kajusK/Darkstar-Mk.II/avr/src/modes/caving.c

/*
 * Caving mode
 *
 * For license, see LICENSE.txt
 *
 * Jakub Kaderka 2017
 */

#include <inttypes.h>
#include <string.h>

#include "system.h"
#include "buttons.h"
#include "light.h"

struct s_levels {
	uint8_t flood;
	uint8_t spot;
	uint8_t red;
	uint8_t white;
};

struct s_config {
	uint16_t magic;
	uint8_t num_levels;
	uint8_t prg_locked : 1;
	uint8_t light_control : 2;
};

enum e_mode {
	NORMAL,
	PROGRAMMING,
	LOCKED,
	CONFIGURATION,
	CONFIGURATION_ENTRY,	//entering config mode, ignore buttons
};

#define BUTTON_UP BUTTON1
#define BUTTON_DOWN BUTTON2

//time in tenths of ms to be considered as holding
#define HOLD_TIME 50

//time spent in mode=0 to go to sleep
#define OFF_TIME 200

//inactivity before returning from programming mode
#define TIMER_MAX 150

//voltage levels to report
#define VOLTAGE_4	3700
#define VOLTAGE_3	3500	//limit 1
#define VOLTAGE_2	3300	//limit 2
#define VOLTAGE_1	3100	//limit 3

//temperature limits
#define TEMP_LIM_START	40	//enable limiting above this temperature
#define TEMP_LIM_AGGRESIVE	45	//limit more aggresive above this temperature
#define TEMP_LIM_MIN	30	//don't limit below this level

//minimum settable light level
#define LIGHT_MIN 1
//increase by this value in programming mode
#define LIGHT_STEP 50

#define DEF_LEVELS 7
#define MAX_LEVELS 10

// magic value to determine if config is already in eeprom
#define MAGIC 0xBEEF

const struct s_levels def_levels[] = {{0, 0, 0, 0}, // off - must be here
				      {0, 0, 1, 0}, //red only
				      {LIGHT_MIN, 0, 0, 0}, //low spot
				      {LIGHT_STEP, LIGHT_STEP, 0, 0}, //small spaces
				      {100, 50, 0, 0}, //normal walking
				      {70, 200, 0, 0}, //distance
				      {255, 255, 0, 0}}; //photo

//limit levels for low voltage (from lowest to full battery)
const uint8_t limits[5] = {50, 120, 160, 230, 255};

static struct s_levels levels[MAX_LEVELS];
static struct s_config config = { MAGIC, DEF_LEVELS, 0, MODE_NORMAL };

static uint8_t cur_levels;
static enum e_mode cur_mode;

static uint8_t hold_done;
static uint8_t timer;

static void config_load(void)
{
	int i;

	config_read(0, (uint8_t *)&config, sizeof(config));
	config_read(sizeof(config), (uint8_t *)&levels, sizeof(levels[0])*config.num_levels);

	//if mode is completely empty (e.g. corrupted memory), turn flood on
	for (i = 1; i < config.num_levels; i++) {
		if (levels[i].white == 0 && levels[i].red == 0 && levels[i].flood == 0 && levels[i].spot == 0)
			levels[i].flood = LIGHT_MIN;
	}
}

static void config_save(void)
{
	config_write(0, (uint8_t *)&config, sizeof(config));
	config_write(sizeof(config), (uint8_t *)&levels, sizeof(levels[0])*config.num_levels);
}

static void config_default(void)
{
	memcpy(&levels, &def_levels, DEF_LEVELS*sizeof(def_levels[0]));
	config.num_levels = DEF_LEVELS;
	config_save();
}

/*
 * Get current voltage rating
 */
static uint8_t rate_voltage(void)
{
	uint16_t voltage = system_voltage();

	if (voltage < VOLTAGE_1)
		return 0;
	else if (voltage < VOLTAGE_2)
		return 1;
	else if (voltage < VOLTAGE_3)
		return 2;
	else if (voltage < VOLTAGE_4)
		return 3;
	else
		return 4;
}

/*
 * Check if supply voltage is below certain limits, if so, notify user if
 * haven't before
 */
static uint8_t check_voltage(void)
{
	//limit is restarted by changing battery, without this, it would
	//start blinking - voltage jumps back up when current is reduced
	static uint8_t reported = 4;
	uint8_t level = rate_voltage();

	if (level >= reported)
		return reported;

	reported = level;
	if (reported < 4)
		light_blink(LED_SPOT, 20, 40, 4-reported);

	return reported;
}

/*
 * Reduce output power when overheating
 */
static uint8_t heat_limit(void)
{
	int8_t temp = system_temp();
	uint8_t tmp;

	if (temp < TEMP_LIM_START)
		return 255;

	if (temp < TEMP_LIM_AGGRESIVE)
		return 255 - (temp - TEMP_LIM_START + 1)*4;

	tmp = (temp-TEMP_LIM_AGGRESIVE)*8;
	if (tmp + TEMP_LIM_MIN > 128)
		return TEMP_LIM_MIN;
	return 128 - tmp;
}

inline static uint8_t level_next(uint8_t level_cur)
{
	if (level_cur > 255-LIGHT_STEP)
		return 0;
	if (level_cur == 0)
		return LIGHT_MIN;
	return level_cur + LIGHT_STEP;
}

static void mode_programming(void)
{
	if (cur_levels == 0) {
		cur_mode = NORMAL;
		return;
	}

	if (button_state(BUTTON_UP) == BUTTON_JUST_RELEASED &&
	    button_pressed_time(BUTTON_UP) <= HOLD_TIME)
		levels[cur_levels].flood = level_next(levels[cur_levels].flood);

	if (button_state(BUTTON_DOWN) == BUTTON_JUST_RELEASED &&
	    button_pressed_time(BUTTON_DOWN) <= HOLD_TIME)
		levels[cur_levels].spot = level_next(levels[cur_levels].spot);

	if (button_state(BUTTON_DOWN) == BUTTON_PRESSED &&
	    button_pressed_time(BUTTON_DOWN) >= HOLD_TIME && !hold_done) {
		hold_done = 1;
		levels[cur_levels].red = levels[cur_levels].red == 1 ? 0 : 1;
	}
	if (button_state(BUTTON_UP) == BUTTON_PRESSED &&
	    button_pressed_time(BUTTON_UP) >= HOLD_TIME && !hold_done) {
		hold_done = 1;
		levels[cur_levels].white = levels[cur_levels].white == 1 ? 0 : 1;
	}

	if (button_state(BUTTON_UP) == BUTTON_RELEASED &&
	    button_state(BUTTON_DOWN) == BUTTON_RELEASED) {
		hold_done = 0;
		timer++;
		if (timer > TIMER_MAX) {
			cur_mode = NORMAL;
			light_blink(LED_SPOT, 50, 100, 1);

			//if nothing is set, turn on flood
			if (levels[cur_levels].red == 0 &&
			    levels[cur_levels].white == 0 &&
			    levels[cur_levels].flood == 0 &&
			    levels[cur_levels].spot == 0)
				levels[cur_levels].flood = LIGHT_MIN;

			config_save();
			return;
		}
	} else {
		timer = 0;
	}

	if (light_get_blink_finished()) {
		light_set(LED_FLOOD, levels[cur_levels].flood, MODE_NORMAL);
		light_set(LED_SPOT, levels[cur_levels].spot, MODE_NORMAL);
		light_set(LED_RED, levels[cur_levels].red, MODE_NORMAL);
		light_set(LED_WHITE, levels[cur_levels].white, MODE_NORMAL);
	}
}

/*
 * Setup number of modes, programming mode, lock enable
 */
static void mode_config(void)
{
	static uint8_t changed = 0;
	uint8_t i = 0;

	//ignore first button press that is used to enter this mode
	if (cur_mode == CONFIGURATION_ENTRY) {
		light_set(LED_RED, 1, MODE_NORMAL);
		if (button_state(BUTTON_DOWN) != BUTTON_RELEASED)
			return;
		cur_mode = CONFIGURATION;
	}

	if (button_state(BUTTON_UP) == BUTTON_JUST_RELEASED &&
	    button_pressed_time(BUTTON_UP) <= HOLD_TIME) {
		config.num_levels = config.num_levels == MAX_LEVELS ? MAX_LEVELS : config.num_levels+1;
		changed = 1;
	}

	if (button_state(BUTTON_DOWN) == BUTTON_JUST_RELEASED &&
	    button_pressed_time(BUTTON_DOWN) <= HOLD_TIME) {
		config.num_levels = config.num_levels == 1 ? 1 : config.num_levels-1;
		changed = 1;
	}

	if (button_state(BUTTON_UP) == BUTTON_PRESSED &&
	    button_pressed_time(BUTTON_UP) >= HOLD_TIME && !hold_done) {
		hold_done = 1;
		changed = 1;
		//programming mode enable/disable
		if (config.prg_locked) {
			config.prg_locked = 0;
			light_blink(LED_RED, 25, 50, 2);
		} else {
			config.prg_locked = 1;
			light_blink(LED_RED, 25, 50, 1);

		}
	}

	if (button_state(BUTTON_DOWN) == BUTTON_PRESSED &&
	    button_pressed_time(BUTTON_DOWN) >= HOLD_TIME && !hold_done) {
		hold_done = 1;
		light_blink(LED_RED, 25, 50, config.num_levels);
	}

	if (button_state(BUTTON_UP) == BUTTON_RELEASED &&
	    button_state(BUTTON_DOWN) == BUTTON_RELEASED) {
		hold_done = 0;
		timer++;
	} else {
		timer = 0;
	}

	if (changed == 1 && timer == 0xff) {
		for (i = 1; i < config.num_levels; i++) {
			if (levels[i].white == 0 && levels[i].red == 0 && levels[i].spot == 0 && levels[i].flood == 0) {
				levels[i].spot = 50;
				levels[i].red = i % 2;
			}
		}
		changed = 0;
		config_save();
	}
}

/*
 * Transport lock, sweep knob back and forth to disable
 */
static void mode_locked(void)
{
	static uint8_t latest = 0;

	if (button_state(BUTTON_UP) == BUTTON_JUST_RELEASED &&
	  button_pressed_time(BUTTON_UP) < HOLD_TIME) {
		latest = (latest << 2) | 0x03;
		timer = 0;
	} else if (button_state(BUTTON_DOWN) == BUTTON_JUST_RELEASED &&
	   button_pressed_time(BUTTON_DOWN) < HOLD_TIME) {
		latest <<= 2;
		timer = 0;
	}

	//waiting for 11001100
	if (latest == 0xCC) {
		cur_mode = NORMAL;
		cur_levels = 1;
		timer = 0;
		latest = 0;
	}
	//reset if buttons not touched for 2,55 seconds
	if (++timer == 0xff) {
		latest = 0;
		power_off(BUTTON_UP|BUTTON_DOWN);
	}
}

/*
 * Usual lamp operations
 */
static void mode_normal(void)
{
	if (button_state(BUTTON_UP) == BUTTON_JUST_RELEASED &&
	    button_pressed_time(BUTTON_UP) <= HOLD_TIME)
		cur_levels = (cur_levels + 1)%config.num_levels;

	if (button_state(BUTTON_DOWN) == BUTTON_JUST_RELEASED &&
	    button_pressed_time(BUTTON_DOWN) <= HOLD_TIME)
		cur_levels = cur_levels == 0 ? config.num_levels - 1: cur_levels-1;

	if (button_state(BUTTON_DOWN) == BUTTON_PRESSED &&
	    button_pressed_time(BUTTON_DOWN) >= HOLD_TIME && !hold_done) {
		hold_done = 1;
		//lamp off and holding - enable transport lock
		if (cur_levels == 0) {
			cur_mode = LOCKED;
			light_blink(LED_SPOT, 30, 60, 3);
		//turn lamp off
		} else {
			cur_levels = 0;
		}
	}

	if (button_state(BUTTON_UP) == BUTTON_PRESSED &&
	    button_pressed_time(BUTTON_UP) >= HOLD_TIME && !hold_done) {
		hold_done = 1;
		if (cur_levels == 0) {
			//blink voltage level
			light_blink(LED_SPOT, 20, 40, rate_voltage()+1);
		} else if (config.prg_locked == 0) {
			cur_mode = PROGRAMMING;
			light_blink(LED_SPOT, 30, 60, 1);
		}
	}

	if (button_state(BUTTON_UP) == BUTTON_RELEASED &&
	    button_state(BUTTON_DOWN) == BUTTON_RELEASED)
		hold_done = 0;

	//apply changes from above
	if (light_get_blink_finished()) {
		light_set(LED_FLOOD, levels[cur_levels].flood, MODE_NORMAL);
		light_set(LED_SPOT, levels[cur_levels].spot, MODE_NORMAL);
		light_set(LED_RED, levels[cur_levels].red, MODE_NORMAL);
		light_set(LED_WHITE, levels[cur_levels].white, MODE_NORMAL);

		if (cur_levels != 0) {
			uint8_t min = limits[check_voltage()];
			uint8_t tmp = heat_limit();
			min = tmp < min ? tmp : min;
			light_set_limit(min);
		}
	}

	//turn off lamp if all leds are of for more than OFF_TIME
	if (cur_levels == 0 && button_state(BUTTON_DOWN) == BUTTON_RELEASED &&
	    button_state(BUTTON_UP) == BUTTON_RELEASED &&
	    light_get_blink_finished()) {
		timer++;
		if (timer > OFF_TIME) {
			power_off(BUTTON_UP|BUTTON_DOWN);
			timer = 0;
		}
	} else {
		timer = 0;
	}
}

/*
 * This function will be called after connecting power to headlamp
 */
void init(void)
{
	uint16_t magic;

	config_read(0, (uint8_t *)&magic, 2);
	if (magic != MAGIC)
		config_default();
	else
		config_load();

	cur_levels = 0;
	cur_mode = NORMAL;
	hold_done = 0;
	timer = 0;

	if (button_state(BUTTON_DOWN) == BUTTON_PRESSED)
		cur_mode = CONFIGURATION_ENTRY;
}


/*
 * This function is called periodically every 10ms
 *
 * It can't be blocking, just sweep throught as fast as possible
 */
void loop(void)
{
	switch (cur_mode) {
	case PROGRAMMING:
		mode_programming();
		break;
	case LOCKED:
		mode_locked();
		break;
	case CONFIGURATION_ENTRY:
	case CONFIGURATION:
		mode_config();
		break;
	default:
		mode_normal();
		break;
	}
}
